LuckyResistor/PetFeeder6/mechanics/LR2051-402A.stl

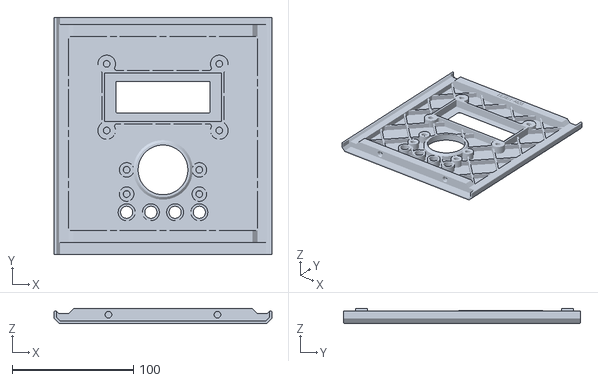
[picture p14: CAD file, 2021-01-24]
mechanics/LR2051-402A.stl
180.0 x 195.9 x 12.0
