LuckyResistor/PetFeeder6/mechanics/LR2051-405A.stl

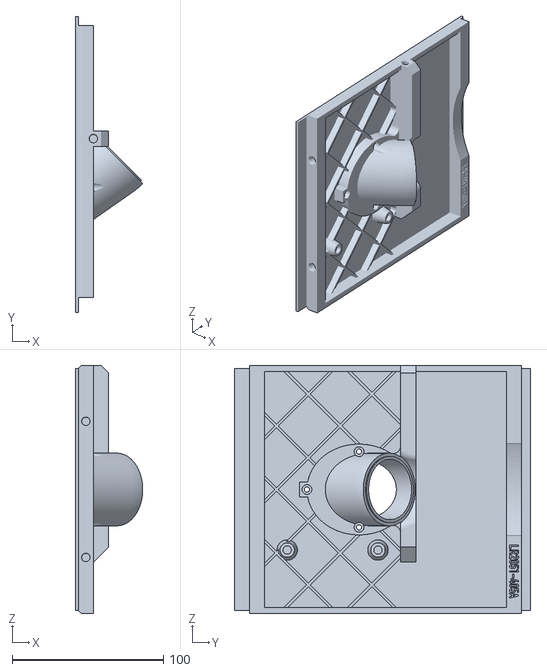
[picture p15: CAD file, 2021-01-12]
mechanics/LR2051-405A.stl
44.6 x 195.9 x 163.9
