LuckyResistor/PetFeeder6/mechanics/LR2051-404A.stl

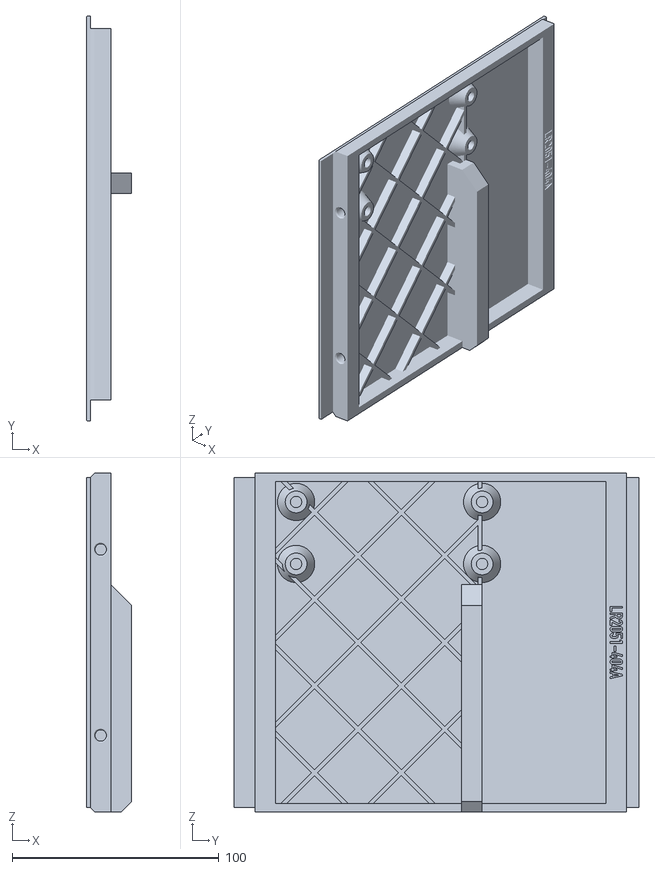
[picture p16: CAD file, 2021-01-12]
mechanics/LR2051-404A.stl
22.0 x 195.9 x 163.9
