LuckyResistor/PetFeeder6/mechanics/LR2051-406A.stl

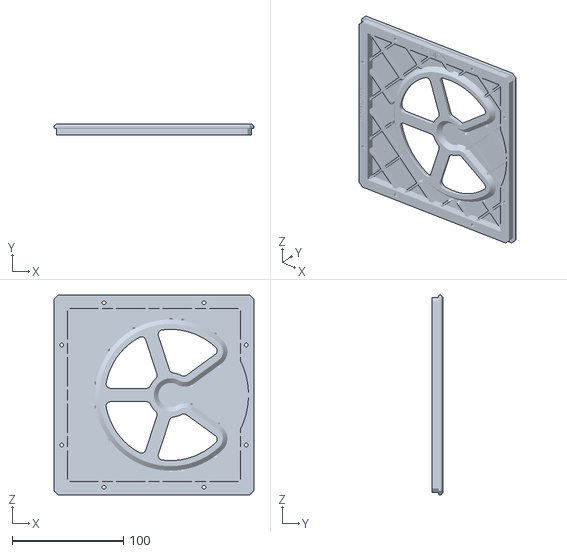
[picture p17: CAD file, 2021-01-12]
mechanics/LR2051-406A.stl
180.0 x 9.95 x 180.0
