LuckyResistor/PetFeeder6/mechanics/LR2051-407A.stl

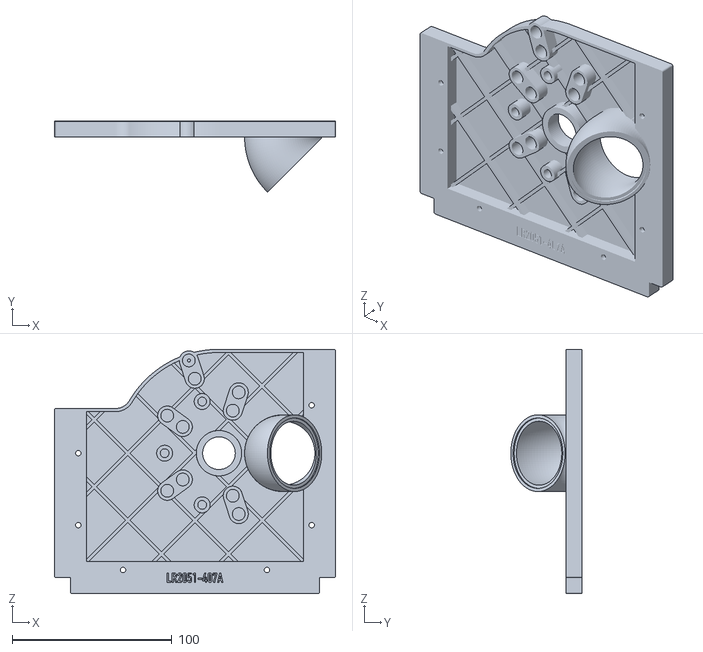
[picture p18: CAD file, 2021-01-12]
mechanics/LR2051-407A.stl
175.8 x 44.6 x 152.9
