LuckyResistor/PetFeeder6/mechanics/LR2051-408A.stl

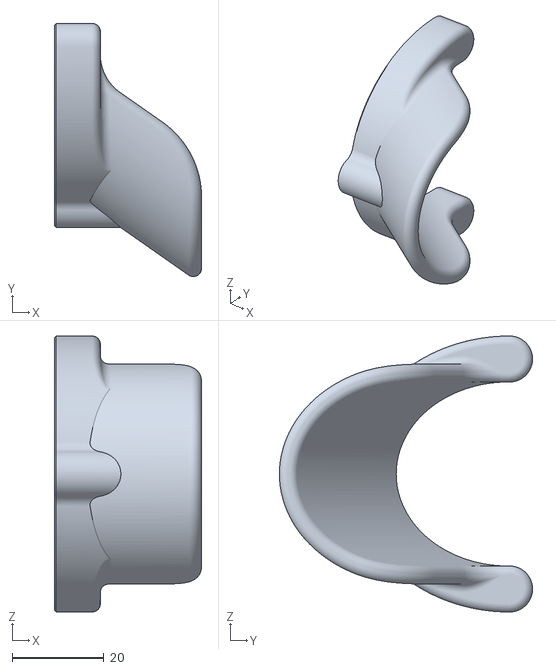
[picture p19: CAD file, 2021-01-12]
mechanics/LR2051-408A.stl
32.0 x 55.0 x 60.0
