LuckyResistor/PetFeeder6/mechanics/LR2051-124.stl

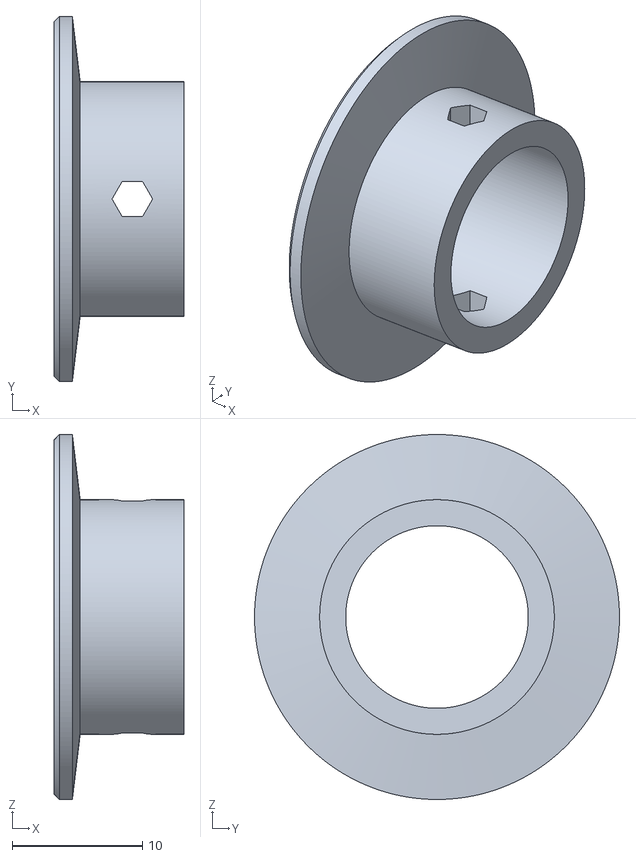
[picture p20: CAD file, 2021-01-02]
mechanics/LR2051-124.stl
9.95 x 28.0 x 28.0
