LuckyResistor/PetFeeder6/mechanics/LR2051-102B.stl

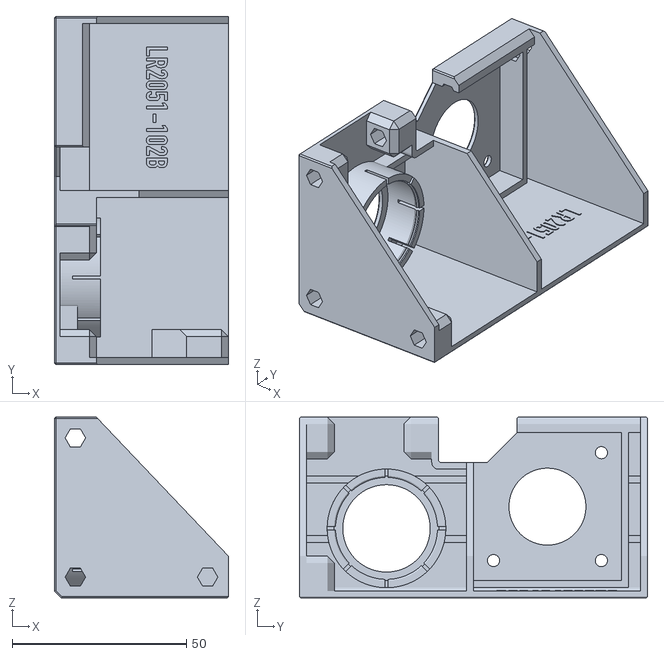
[picture p21: CAD file, 2021-01-02]
mechanics/LR2051-102B.stl
50.0 x 100.0 x 52.0
