LuckyResistor/PetFeeder6/mechanics/LR2051-104B.stl

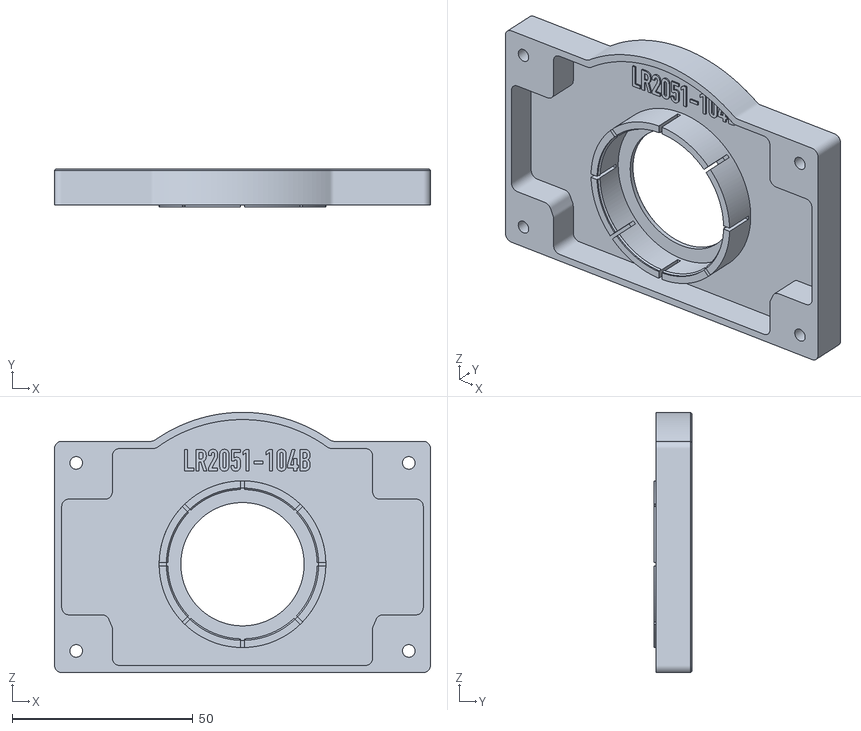
[picture p22: CAD file, 2021-01-02]
mechanics/LR2051-104B.stl
104.0 x 10.6 x 72.0
