LuckyResistor/PetFeeder6/mechanics/LR2051-121.stl

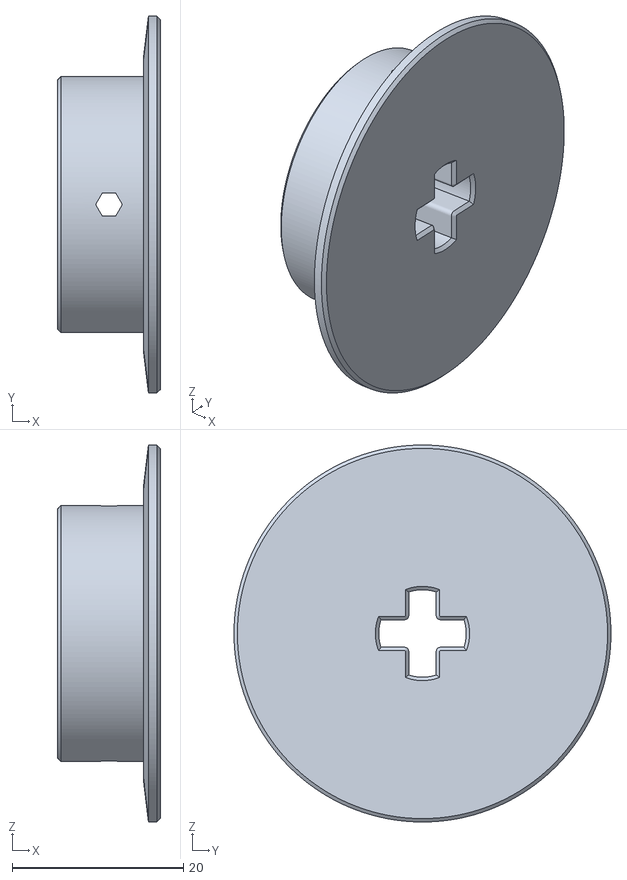
[picture p23: CAD file, 2021-01-02]
mechanics/LR2051-121.stl
12.0 x 44.0 x 44.0
