LuckyResistor/PetFeeder6/mechanics/LR2051-101B.stl

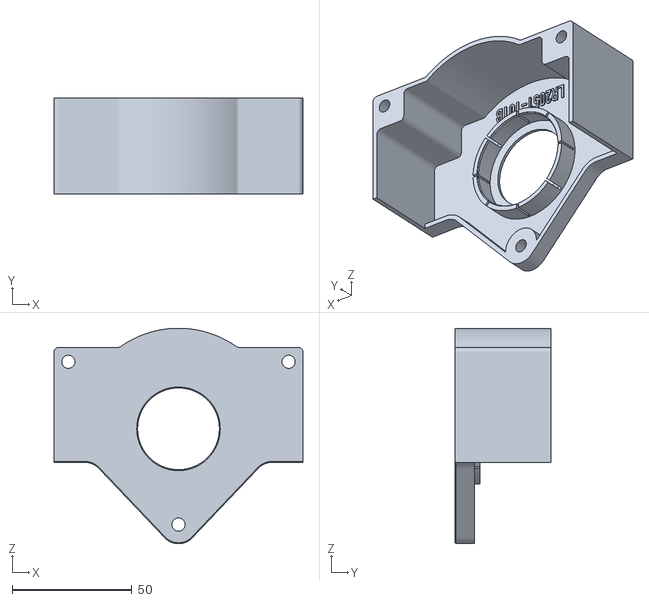
[picture p24: CAD file, 2021-01-02]
mechanics/LR2051-101B.stl
104.0 x 40.0 x 90.0
