LuckyResistor/PetFeeder6/mechanics/LR2051-401A.stl

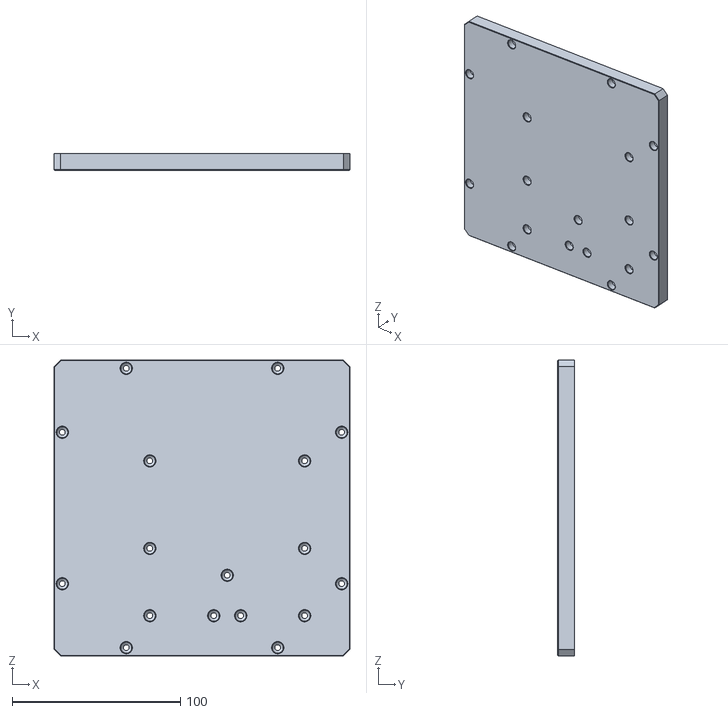
[picture p25: CAD file, 2021-01-02]
mechanics/LR2051-401A.stl
175.9 x 10.0 x 175.9
