LuckyResistor/PetFeeder6/mechanics/LR2051-122.stl

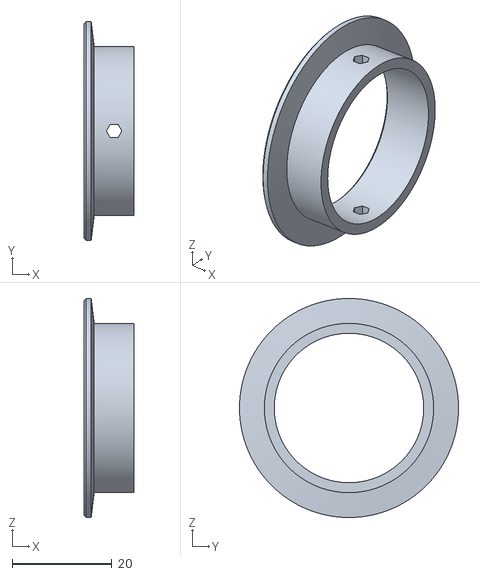
[picture p26: CAD file, 2021-01-02]
mechanics/LR2051-122.stl
9.95 x 44.0 x 44.0
