LuckyResistor/PetFeeder6/mechanics/LR2051-107B.stl

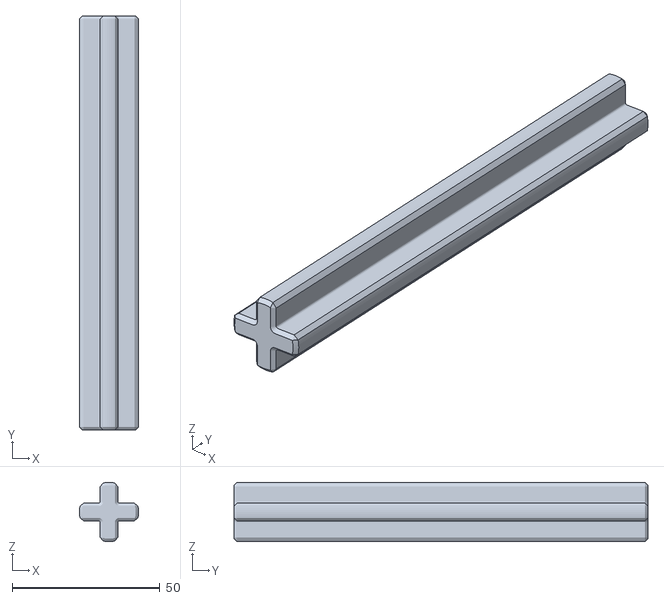
[picture p27: CAD file, 2021-01-02]
mechanics/LR2051-107B.stl
20.0 x 140.0 x 20.0
