LuckyResistor/PetFeeder6/mechanics/LR2051-108B.stl

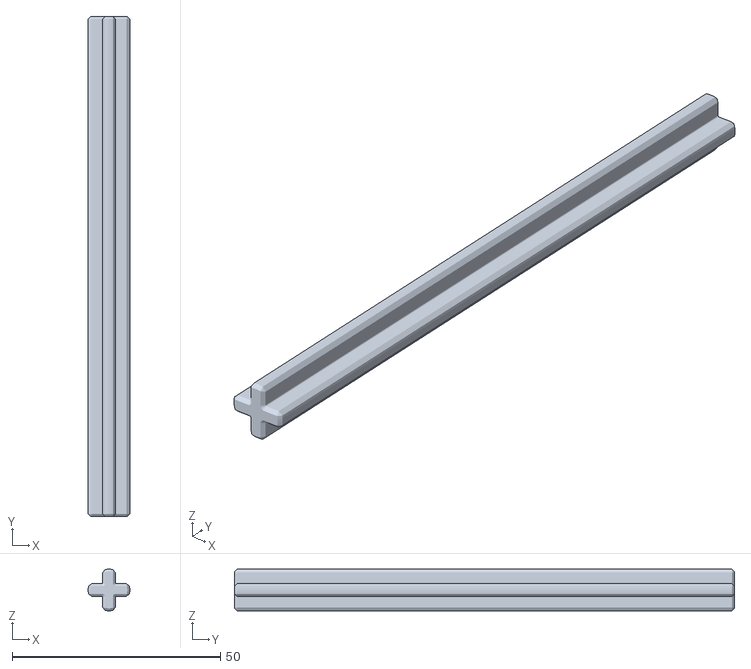
[picture p28: CAD file, 2021-01-02]
mechanics/LR2051-108B.stl
10.0 x 120.0 x 10.0
