LuckyResistor/PetFeeder6/mechanics/LR2051-123.stl

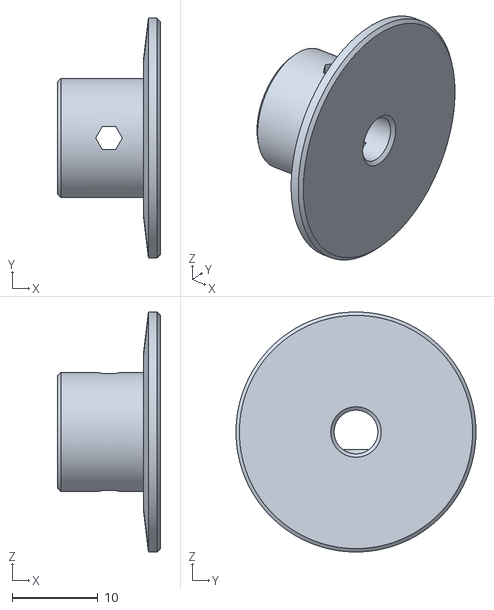
[picture p29: CAD file, 2021-01-02]
mechanics/LR2051-123.stl
12.0 x 28.0 x 28.0
