LuckyResistor/PetFeeder6/mechanics/LR2051-112B.stl

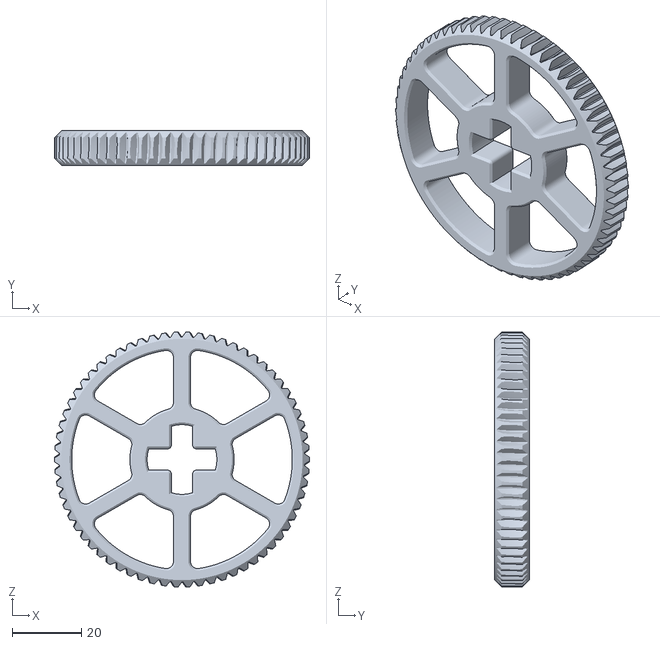
[picture p30: CAD file, 2021-01-02]
mechanics/LR2051-112B.stl
73.9 x 10.0 x 73.9
