LuckyResistor/PetFeeder6/mechanics/LR2051-105B.stl

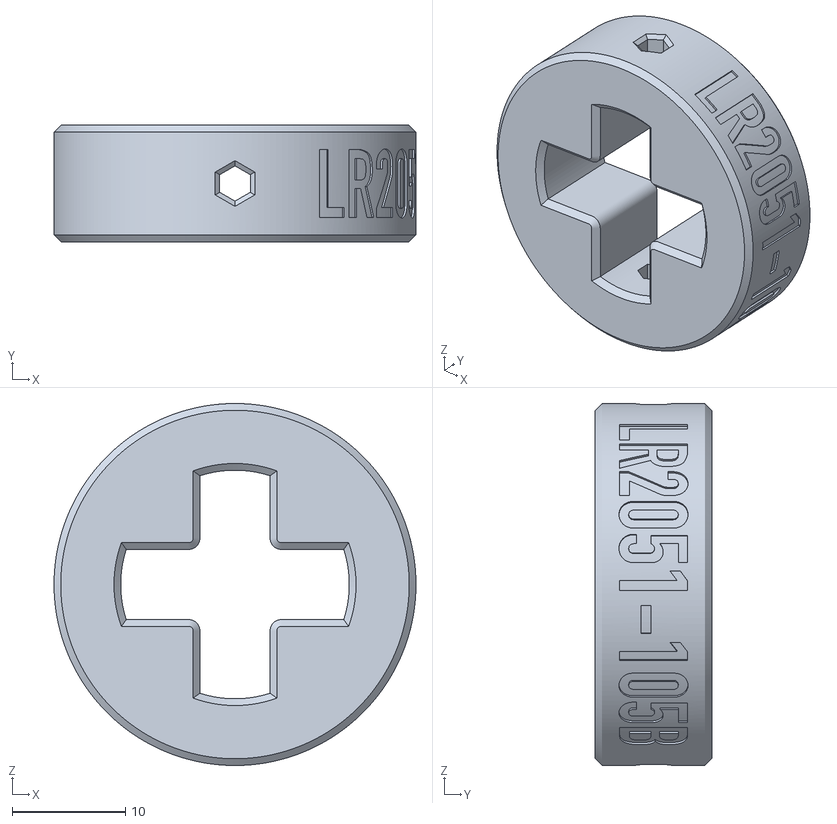
[picture p31: CAD file, 2021-01-02]
mechanics/LR2051-105B.stl
32.0 x 10.3 x 32.0
