LuckyResistor/PetFeeder6/mechanics/LR2051-103B.stl

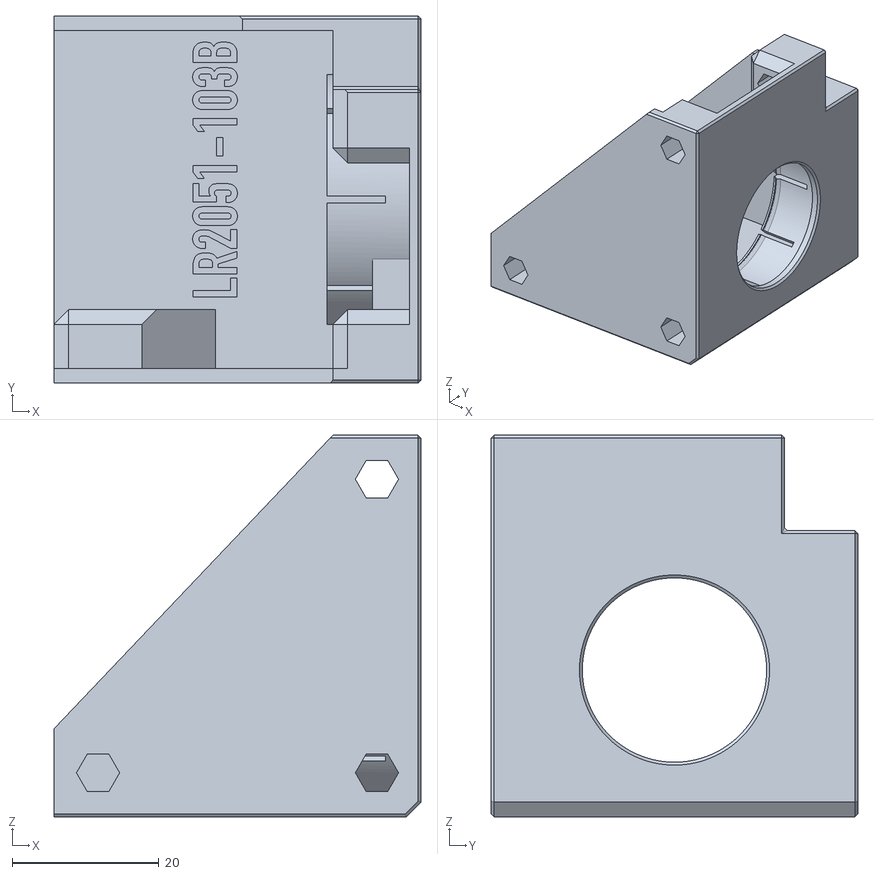
[picture p32: CAD file, 2021-01-02]
mechanics/LR2051-103B.stl
50.0 x 50.0 x 52.0
