LuckyResistor/PetFeeder6/mechanics/LR2051-111B.stl

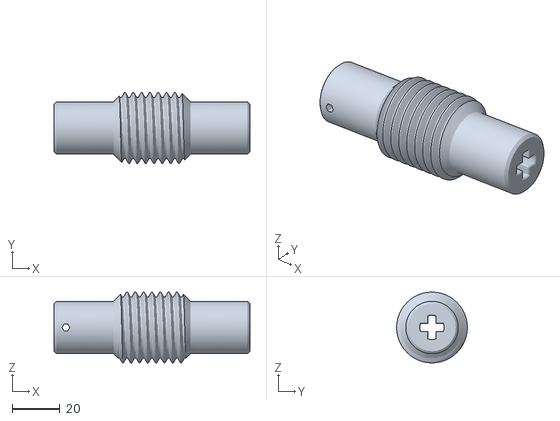
[picture p33: CAD file, 2021-01-02]
mechanics/LR2051-111B.stl
82.4 x 29.7 x 29.7
